bidouilleurs/routeur_solaire/src/regulation.h

/***************************************/
/******** pilotage et regulation   ********/
/***************************************/
#ifndef RA_REGULATION_H
#define RA_REGULATION_H
class RARegulationClass
{

public:
  int mesureDerive(float x, float seuil);

  int regulGrad(int dev);

  /**************************************/
  /******** Pilotage exterieur*******/
  /**************************************/
  void pilotage();
  void desactivation();
};
extern RARegulationClass RARegulation;
#endif
